golanaa/sourcerer/hardware/pcb/microcontroller.kicad_sch

## KiCad design hardware/pcb/microcontroller.kicad_sch (2026-09-09)

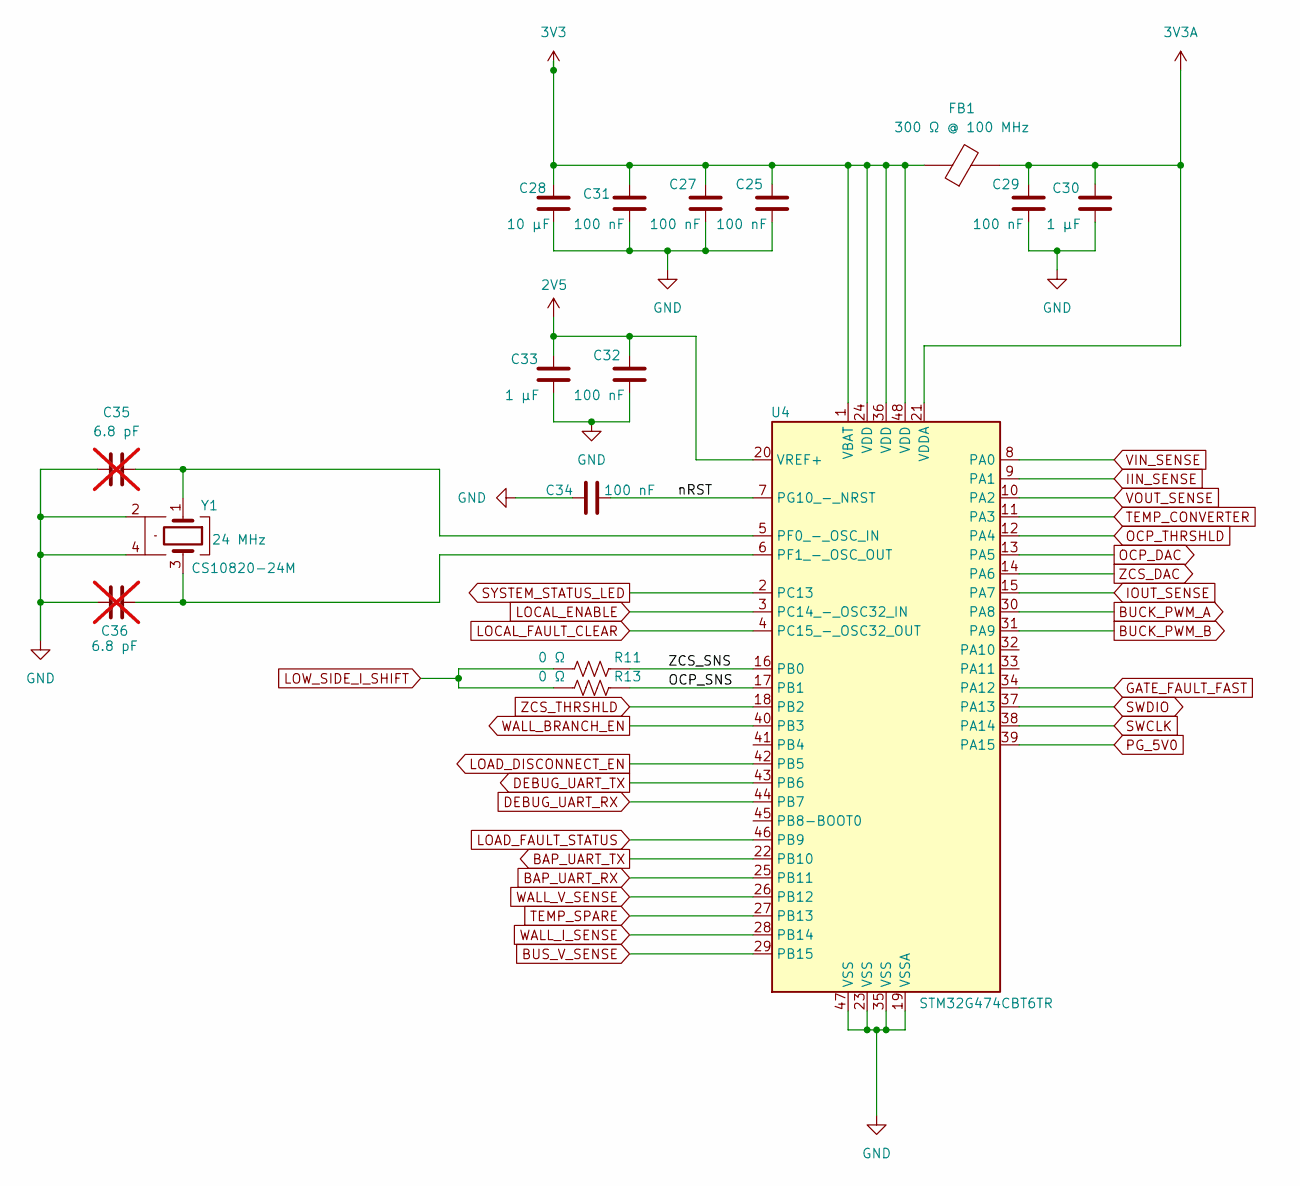
[picture p2: schematic microcontroller.kicad_sch]

Parts:
C25, C27, C28, C29, C32, C34: 100 nF; C_0603_1608Metric; Voltage Rating 25 V; Tolerance ±10%
C30, C33: 1 µF; C_0805_2012Metric; Voltage Rating 25 V; Tolerance ±10%
C31: 10 µF; C_0805_2012Metric; Voltage Rating 10 V; Tolerance ±10%
C35, C36: 6.8 pF; C_0402_1005Metric; Voltage Rating 50 V; Tolerance ±5%; not fitted
FB1: 300 Ω @ 100 MHz; FCM1608KF-301T05_PCB; Tolerance ±25%; Manufacturer Part Numbe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 FCM1608KF-301T05
R11, R13: 0 Ω; R_0402_1005Metric; Tolerance N/A (jumper; maximum resistance governs); Power Rating 62.5 mW
U4: STM32G474CBT6TR; STM32G474CBT6TR_PCB; Manufacturer Part Numbe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 STM32G474CBT6TR
Y1: CS10820-24M; CS10820-24M_PCB; Frequency Tolerance ±20 ppm; Manufacturer Part Numbe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 CS10820-24M

Connections:
2V5: C32.1, C33.1, U4.20 (VREF+)
3V3: C25.1, C27.1, C28.1, C31.1, FB1.1, U4.1 (VBAT), U4.24 (VDD), U4.36 (VDD), U4.48 (VDD)
3V3A: C29.1, C30.1, FB1.2, U4.21 (VDDA)
BAP_UART_RX: U4.25 (PB11)
BAP_UART_TX: U4.22 (PB10)
BUCK_PWM_A: U4.30 (PA8)
BUCK_PWM_B: U4.31 (PA9)
BUS_V_SENSE: U4.29 (PB15)
DEBUG_UART_RX: U4.44 (PB7)
DEBUG_UART_TX: U4.43 (PB6)
GATE_FAULT_FAST: U4.34 (PA12)
GND: C25.2, C27.2, C28.2, C29.2, C30.2, C31.2, C32.2, C33.2, C34.2, C35.1, C36.1, U4.19 (VSSA), U4.23 (VSS), U4.35 (VSS), U4.47 (VSS), Y1.2 (G), Y1.4 (G)
IIN_SENSE: U4.9 (PA1)
IOUT_SENSE: U4.15 (PA7)
LOAD_DISCONNECT_EN: U4.42 (PB5)
LOAD_FAULT_STATUS: U4.46 (PB9)
LOCAL_ENABLE: U4.3 (PC14_-_OSC32_IN)
LOCAL_FAULT_CLEAR: U4.4 (PC15_-_OSC32_OUT)
LOW_SIDE_I_SHIFT: R11.1, R13.1
unnamed: C35.2, U4.5 (PF0_-_OSC_IN), Y1.1
unnamed: C36.2, U4.6 (PF1_-_OSC_OUT), Y1.3
OCP_DAC: U4.13 (PA5)
OCP_SNS: R13.2, U4.17 (PB1)
OCP_THRSHLD: U4.12 (PA4)
PG_5V0: U4.39 (PA15)
SWCLK: U4.38 (PA14)
SWDIO: U4.37 (PA13)
SYSTEM_STATUS_LED: U4.2 (PC13)
TEMP_CONVERTER: U4.11 (PA3)
TEMP_SPARE: U4.27 (PB13)
VIN_SENSE: U4.8 (PA0)
VOUT_SENSE: U4.10 (PA2)
WALL_BRANCH_EN: U4.40 (PB3)
WALL_I_SENSE: U4.28 (PB14)
WALL_V_SENSE: U4.26 (PB12)
ZCS_DAC: U4.14 (PA6)
ZCS_SNS: R11.2, U4.16 (PB0)
ZCS_THRSHLD: U4.18 (PB2)
nRST: C34.1, U4.7 (PG10_-_NRST)
