golanaa/sourcerer/hardware/pcb/power.kicad_sch

## KiCad design hardware/pcb/power.kicad_sch (2026-09-09)

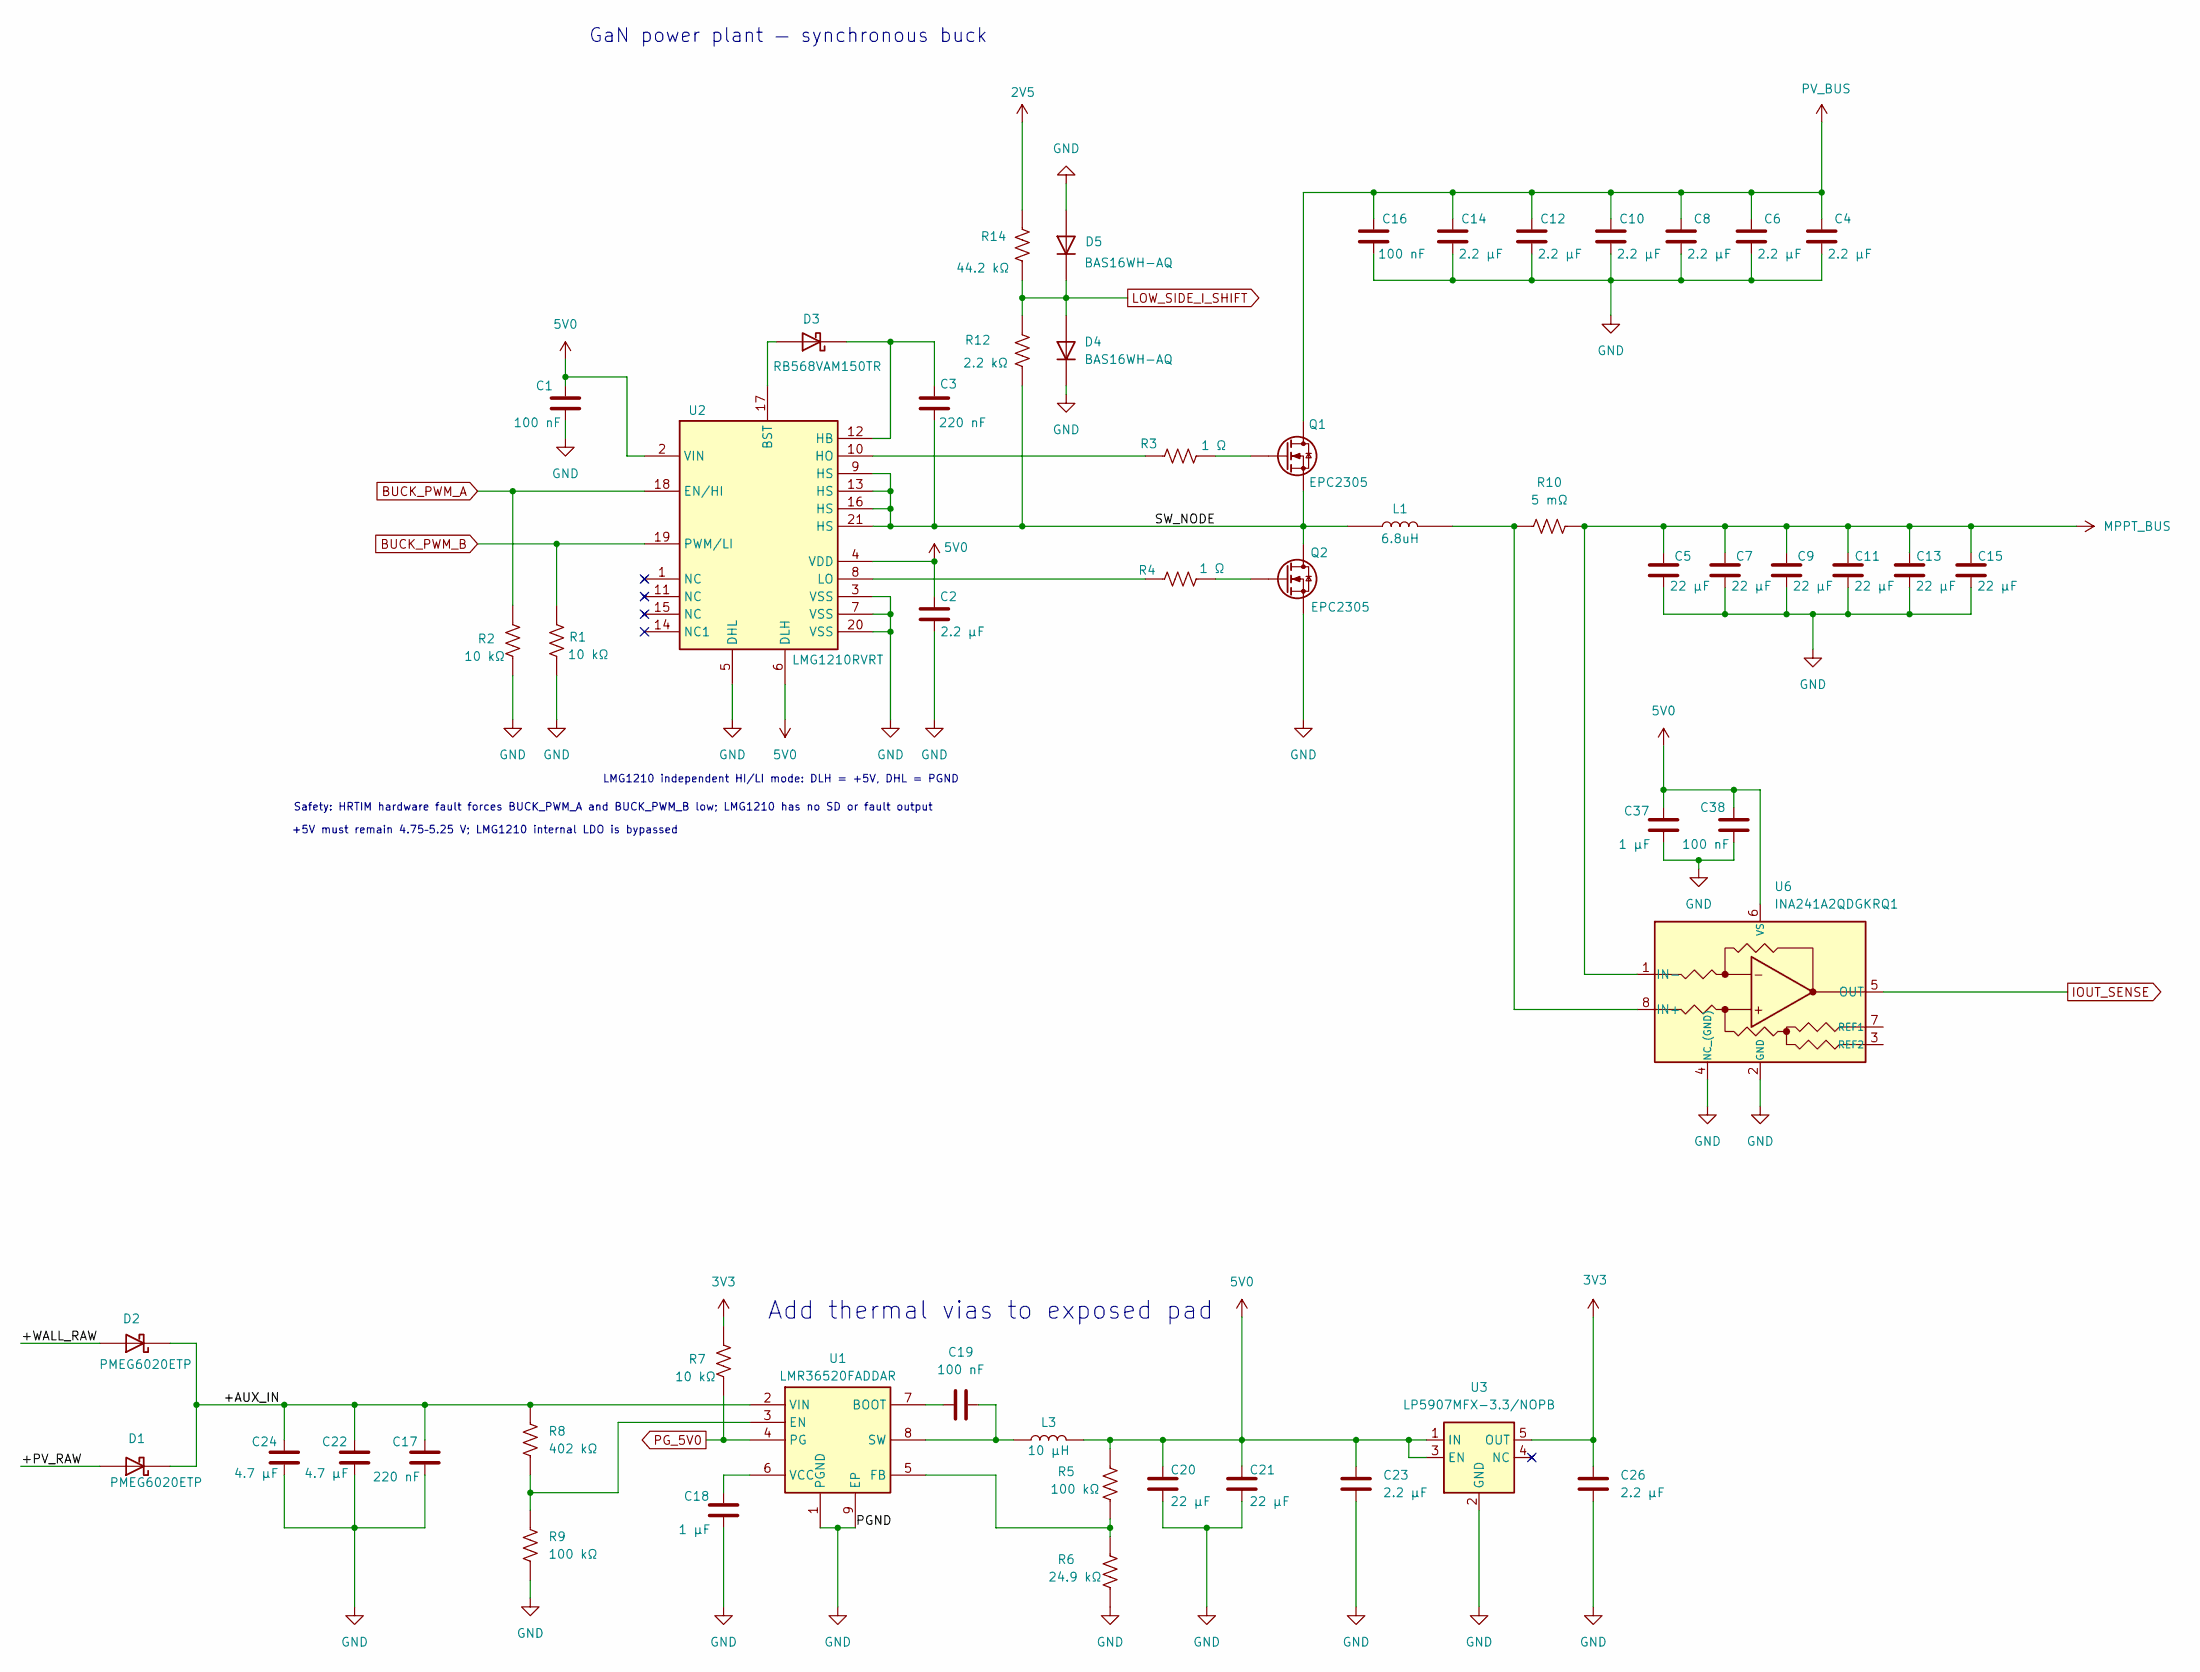
[picture p3: schematic power.kicad_sch]

Parts:
C1, C19, C38: 100 nF; C_0603_1608Metric; Voltage Rating 25 V; Tolerance ±10%
C2, C23, C26: 2.2 µF; C_0805_2012Metric; Voltage Rating 10 V; Tolerance ±10%
C3: 220 nF; C_0603_1608Metric; Voltage Rating 16 V; Tolerance ±10%
C4, C6, C8, C10, C12, C14: 2.2 µF; C_1210_3225Metric; Voltage Rating 100 V; Tolerance ±10%
C5, C7, C9, C11, C13, C15, C20, C21: 22 µF; C_1210_3225Metric; Voltage Rating 25 V; Tolerance ±10%
C16: 100 nF; C_0805_2012Metric; Voltage Rating 100 V; Tolerance ±10%
C17: 220 nF; C_0805_2012Metric; Voltage Rating 100 V; Tolerance ±10%
C18, C37: 1 µF; C_0805_2012Metric; Voltage Rating 25 V; Tolerance ±10%
C22, C24: 4.7 µF; C_1210_3225Metric; Voltage Rating 100 V; Tolerance ±10%
D1, D2: PMEG6020ETP; PMEG6020ETP_PCB; Manufacturer Part Numbe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 PMEG6020ETP
D3: RB568VAM150TR; RB568VAM150TR_PCB; Manufacturer Part Numbe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 RB568VAM150TR
D4, D5: BAS16WH-AQ; BAS16WH-AQ_PCB; Manufacturer Part Numbe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 BAS16WH-AQ
L1: 6.8uH; XAL1010-682MED_PCB; Manufacturer Part Numbe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 XAL1010-682MED
L3: 10 µH; IHLP2525CZER100M01_PCB; Tolerance ±20%; Heat Rating Current 3 A; Manufacturer Part Numbe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 IHLP2525CZER100M01
Q1, Q2: EPC2305; EPC2305_PCB; Manufacturer Part Numbe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 EPC2305
R1, R2, R7: 10 kΩ; R_0402_1005Metric; Tolerance ±1%; Power Rating 62.5 mW
R3, R4: 1 Ω; R_0402_1005Metric; Tolerance ±1%; Power Rating 62.5 mW
R5: 100 kΩ; R_0402_1005Metric; Tolerance ±1%; Power Rating 62.5 mW
R6: 24.9 kΩ; R_0402_1005Metric; Tolerance ±1%; Power Rating 62.5 mW
R8: 402 kΩ; R_0805_2012Metric; Tolerance ±0.1%; Power Rating 125 mW
R9: 100 kΩ; R_0805_2012Metric; Tolerance ±0.1%; Power Rating 125 mW
R10: 5 mΩ; SEWF3920D5L00P9_PCB; Tolerance ±0.5%; Power Rating 3 W; Manufacturer Part Numbe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 SEWF3920D5L00P9
R12: 2.2 kΩ; R_2010_5025Metric; Tolerance ±1%; Power Rating 1 W
R14: 44.2 kΩ; R_0402_1005Metric; Tolerance ±0.1%; Power Rating 62.5 mW
U1: LMR36520FADDAR; LMR36520FADDAR_PCB; Manufacturer Part Numbe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 LMR36520FADDAR
U2: LMG1210RVRT; LMG1210RVRT_PCB; Manufacturer Part Numbe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 LMG1210RVRT
U3: LP5907MFX-3.3/NOPB; P-00005_PCB; Manufacturer Part Numbe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 LP5907MFX-3.3/NOPB
U6: INA241A2QDGKRQ1; INA241A2QDGKRQ1_PCB; Manufacturer Part Numbe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 INA241A2QDGKRQ1

Connections:
2V5: R14.1
3V3: C26.1, R7.1, U3.5 (OUT)
5V0: C1.1, C2.1, C20.1, C21.1, C23.1, C37.1, C38.1, L3.2, R5.1, U2.2 (VIN), U2.4 (VDD), U2.6 (DLH), U3.1 (IN), U3.3 (EN), U6.6 (VS)
+AUX_IN: C17.1, C22.1, C24.1, D1.1 (K), D2.1 (K), R8.1, U1.2 (VIN)
+PV_RAW: D1.2 (A)
+WALL_RAW: D2.2 (A)
BUCK_PWM_A: R2.1, U2.18 (EN/HI)
BUCK_PWM_B: R1.1, U2.19 (PWM/LI)
GND: C1.2, C2.2, C4.2, C5.2, C6.2, C7.2, C8.2, C9.2, C10.2, C11.2, C12.2, C13.2, C14.2, C15.2, C16.2, C17.2, C18.2, C20.2, C21.2, C22.2, C23.2, C24.2, C26.2, C37.2, C38.2, D4.1 (K), D5.2 (A), Q2.2 (S), Q2.4 (S), Q2.6 (S), R1.2, R2.2, R6.2, R9.2, U1.1 (PGND), U1.9 (EP), U2.3 (VSS), U2.5 (DHL), U2.7 (VSS), U2.20 (VSS), U3.2 (GND), U6.2 (GND), U6.4 (NC_(GND))
IOUT_SENSE: U6.5 (OUT)
LOW_SIDE_I_SHIFT: D4.2 (A), D5.1 (K), R12.1, R14.2
MPPT_BUS: C5.1, C7.1, C9.1, C11.1, C13.1, C15.1, R10.2, U6.1 (IN-)
unnamed: C3.1, D3.1 (K), U2.12 (HB)
unnamed: C18.1, U1.6 (VCC)
unnamed: C19.1, U1.7 (BOOT)
unnamed: C19.2, L3.1, U1.8 (SW)
unnamed: D3.2 (A), U2.17 (BST)
unnamed: L1.2, R10.1, U6.8 (IN+)
unnamed: Q1.1 (G), R3.2
unnamed: Q2.1 (G), R4.2
unnamed: R3.1, U2.10 (HO)
unnamed: R4.1, U2.8 (LO)
unnamed: R5.2, R6.1, U1.5 (FB)
unnamed: R8.2, R9.1, U1.3 (EN)
PG_5V0: R7.2, U1.4 (PG)
PV_BUS: C4.1, C6.1, C8.1, C10.1, C12.1, C14.1, C16.1, Q1.3 (D), Q1.5 (D), Q1.7 (D)
SW_NODE: C3.2, L1.1, Q1.2 (S), Q1.4 (S), Q1.6 (S), Q2.3 (D), Q2.5 (D), Q2.7 (D), R12.2, U2.9 (HS), U2.13 (HS), U2.16 (HS), U2.21 (HS)

Notes on the sheet:
+5V must remain 4.75–5.25 V; LMG1210 internal LDO is bypassed
GaN power plant — synchronous buck
Safety: HRTIM hardware fault forces BUCK_PWM_A and BUCK_PWM_B low; LMG1210 has no SD or fault output
Add thermal vias to exposed pad
LMG1210 independent HI/LI mode: DLH = +5V, DHL = PGND
